Rohit04121998/mAhTime/PCB_KiCAD/PDF/mAhTime-F.CrtYd.pdf

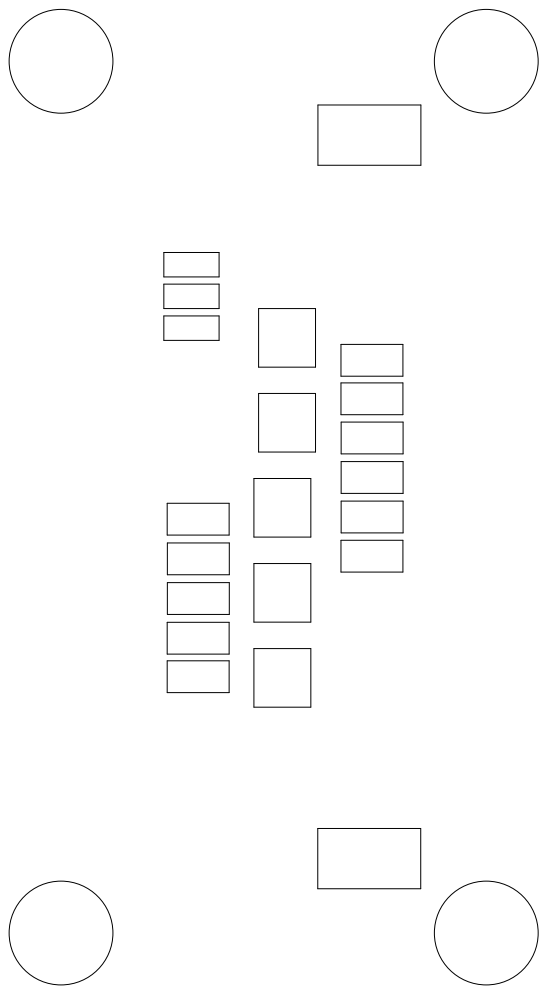
[picture p26: page 1]
