Rohit04121998/mAhTime/PCB_KiCAD/PDF/mAhTime-F.Cu.pdf

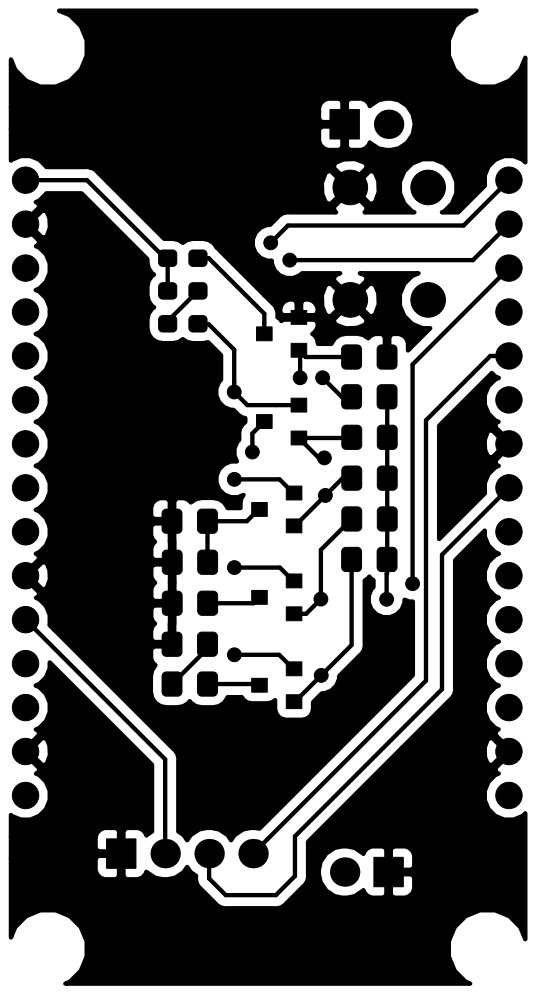
[picture p27: page 1]
