Rohit04121998/mAhTime/PCB_KiCAD/PDF/mAhTime-F.Fab.pdf

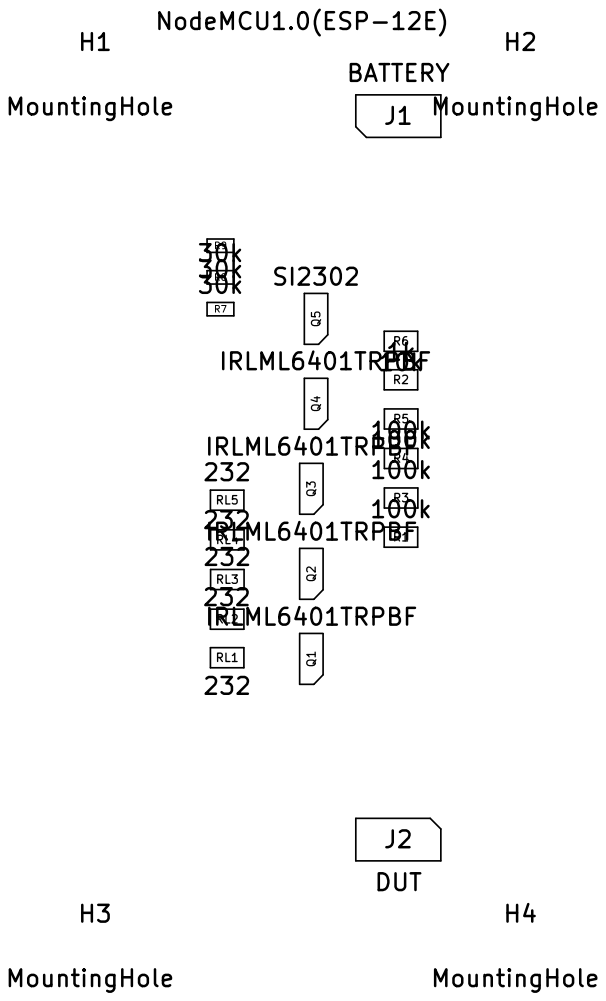
[picture p28: page 1]
