Rohit04121998/mAhTime/PCB_KiCAD/PDF/mAhTime-F.Mask.pdf

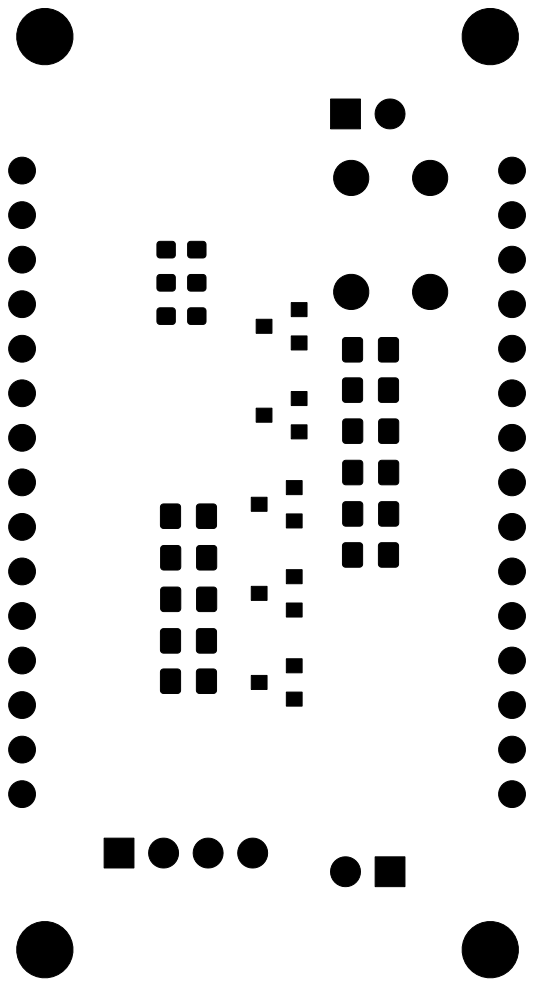
[picture p29: page 1]
