Rohit04121998/mAhTime/PCB_KiCAD/PDF/mAhTime-F.Paste.pdf

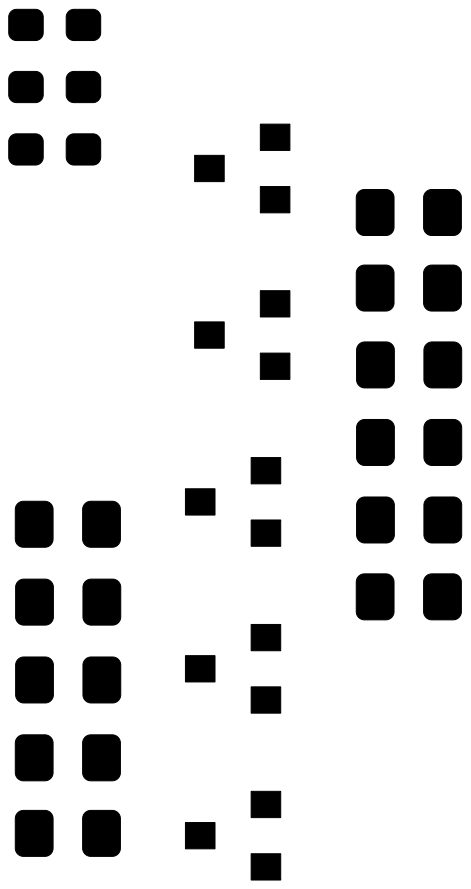
[picture p30: page 1]
