Rohit04121998/mAhTime/PCB_KiCAD/PDF/mAhTime-F.SilkS.pdf

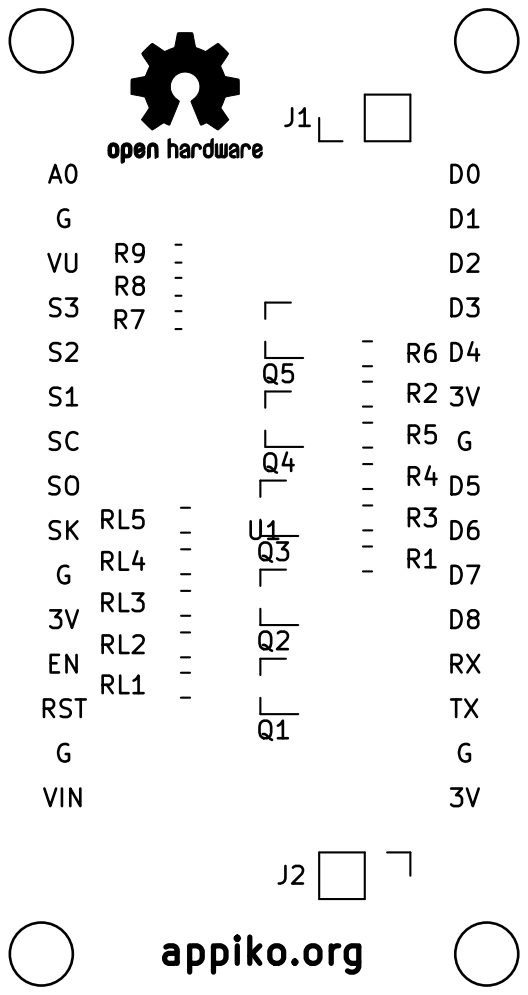
[picture p31: page 1]
