Rohit04121998/mAhTime/upload_voltage/displaySymbols.h

#define logo_width 128
#define logo_height 32
#define ohm_height 12
#define ohm_width 16
#define wifi_height 9
#define wifi_width 16

static const unsigned char PROGMEM logo[]= {      //logo shown during power up
0x00, 0x00, 0x00, 0x03, 0xE0, 0x00, 0x00, 0x00, 0x00, 0x00, 0x00, 0x00, 0x00, 0x00, 0x00, 0x00,
0x00, 0x00, 0x00, 0x1F, 0xF8, 0x00, 0x00, 0x00, 0x00, 0x00, 0x00, 0x00, 0x00, 0x00, 0x00, 0x00,
0x00, 0x00, 0x00, 0x7F, 0xFE, 0x00, 0x00, 0x00, 0x00, 0x00, 0x00, 0x00, 0x00, 0x00, 0x00, 0x00,
0x00, 0x00, 0x01, 0xFF, 0xFF, 0x00, 0x00, 0x00, 0x00, 0x00, 0x00, 0x00, 0x00, 0x00, 0x00, 0x00,
0x00, 0x00, 0x07, 0xC0, 0xFF, 0x80, 0x00, 0x00, 0x00, 0x00, 0x00, 0x00, 0x00, 0x00, 0x00, 0x00,
0x00, 0x00, 0x06, 0x00, 0x3F, 0xC0, 0x00, 0x00, 0x00, 0x00, 0x00, 0x00, 0x00, 0x00, 0x00, 0x00,
0x00, 0x00, 0x0C, 0x00, 0x1F, 0xC0, 0x00, 0x00, 0x00, 0x00, 0x04, 0x30, 0x00, 0x00, 0x00, 0x00,
0x00, 0x00, 0x0F, 0xF8, 0x19, 0xE0, 0x00, 0x00, 0x00, 0x00, 0x0E, 0x30, 0x00, 0x00, 0x00, 0x00,
0x00, 0x00, 0x10, 0x06, 0x19, 0xE0, 0x00, 0x00, 0x00, 0x00, 0x0E, 0x30, 0x00, 0x00, 0x00, 0x00,
0x00, 0x00, 0x00, 0x01, 0x3F, 0xE0, 0x00, 0x00, 0x00, 0x00, 0x00, 0x30, 0x00, 0x00, 0x00, 0x00,
0x00, 0x00, 0x00, 0x00, 0xFF, 0xE0, 0x00, 0x00, 0x00, 0x00, 0x00, 0x30, 0x00, 0x00, 0x00, 0x00,
0x00, 0x00, 0x00, 0x00, 0xFF, 0xE0, 0x0F, 0xC6, 0x78, 0xCF, 0x0E, 0x37, 0x83, 0xE0, 0x00, 0x00,
0x00, 0x00, 0x00, 0x00, 0xFF, 0xE0, 0x1F, 0xE6, 0xFC, 0xDF, 0x8E, 0x3F, 0xC7, 0xF0, 0x00, 0x00,
0x00, 0x00, 0x00, 0x01, 0xFF, 0xE0, 0x38, 0x67, 0x8C, 0xF9, 0x8E, 0x38, 0xCE, 0x38, 0x00, 0x00,
0x00, 0x00, 0x00, 0x01, 0xFF, 0xC0, 0x30, 0x67, 0x0E, 0xE1, 0xCE, 0x31, 0x8C, 0x18, 0x00, 0x00,
0x00, 0x00, 0x00, 0x01, 0xFF, 0xC0, 0x70, 0xC6, 0x06, 0xC0, 0xCE, 0x3F, 0x0C, 0x18, 0x00, 0x00,
0x00, 0x00, 0x00, 0x01, 0xFF, 0xE0, 0x71, 0xC6, 0x0C, 0xC1, 0x8E, 0x33, 0x8C, 0x18, 0x00, 0x00,
0x00, 0x00, 0x00, 0x00, 0xFF, 0xF0, 0x73, 0xC6, 0x1C, 0xC3, 0x8E, 0x31, 0xCE, 0x38, 0x00, 0x00,
0x00, 0x00, 0x00, 0x00, 0xFF, 0x00, 0x3E, 0xE7, 0xF0, 0xFE, 0x07, 0x30, 0xC7, 0xF0, 0x00, 0x00,
0x00, 0x00, 0x00, 0x00, 0xFC, 0x04, 0x0C, 0x47, 0xC0, 0xF8, 0x02, 0x30, 0xC3, 0xE0, 0x00, 0x00,
0x00, 0x00, 0x00, 0x00, 0x78, 0x04, 0x00, 0x03, 0x00, 0x60, 0x00, 0x00, 0x00, 0x00, 0x00, 0x00,
0x00, 0x00, 0x00, 0x00, 0x30, 0x06, 0x00, 0x03, 0x00, 0x60, 0x00, 0x00, 0x00, 0x00, 0x00, 0x00,
0x00, 0x00, 0x00, 0x00, 0x20, 0x0E, 0x00, 0x03, 0x00, 0x60, 0x00, 0x00, 0x00, 0x00, 0x00, 0x00,
0x00, 0x00, 0x00, 0x00, 0x40, 0x1E, 0x00, 0x03, 0x00, 0x60, 0x00, 0x00, 0x00, 0x00, 0x00, 0x00,
0x00, 0x00, 0x00, 0x00, 0x80, 0x3E, 0x00, 0x03, 0x00, 0x60, 0x00, 0x00, 0x00, 0x00, 0x00, 0x00,
0x00, 0x00, 0x00, 0x01, 0x00, 0x7F, 0x00, 0x00, 0x00, 0x00, 0x00, 0x00, 0x00, 0x00, 0x00, 0x00,
0x00, 0x00, 0x00, 0x00, 0xC1, 0xFF, 0x00, 0x00, 0x00, 0x00, 0x00, 0x00, 0x00, 0x00, 0x00, 0x00,
0x00, 0x00, 0x00, 0x00, 0x3F, 0xFF, 0x00, 0x00, 0x00, 0x00, 0x00, 0x00, 0x00, 0x00, 0x00, 0x00,
0x00, 0x00, 0x00, 0x00, 0x01, 0xFF, 0x00, 0x00, 0x00, 0x00, 0x00, 0x00, 0x00, 0x00, 0x00, 0x00,
0x00, 0x00, 0x00, 0x00, 0x00, 0x3F, 0x00, 0x00, 0x00, 0x00, 0x00, 0x00, 0x00, 0x00, 0x00, 0x00,
0x00, 0x00, 0x00, 0x00, 0x00, 0x13, 0x00, 0x00, 0x00, 0x00, 0x00, 0x00, 0x00, 0x00, 0x00, 0x00,
0x00, 0x00, 0x00, 0x00, 0x00, 0x13, 0x00, 0x00, 0x00, 0x00, 0x00, 0x00, 0x00, 0x00, 0x00, 0x00
};

static const unsigned char PROGMEM ohm [] = {     //symbol for ohm
  B00000111, B11100000,
  B00011111, B11111000,
  B00111100, B00111100,
  B01111000, B00011110,
  B01110000, B00001110,
  B01110000, B00001110,
  B00111000, B00011100,
  B00011100, B00111000,
  B00001100, B00110000,
  B10000110, B01100001,
  B11000110, B01100011,
  B11111100, B00111111,
};

static const unsigned char PROGMEM wifi [] = {
  B00000111, B11100000,
  B00001000, B00010000,
  B00010011, B11001000,
  B00000100, B00100000,
  B00000001, B10000000,
  B00000010, B01000000,
  B00000000, B00000000,
  B00000001, B10000000,
  B00000001, B10000000,
};
