Rohit04121998/mAhTime/upload_voltage/DateTime.h

#include <NTPClient.h>
#include <ESP8266WiFi.h>
#include <WiFiUdp.h>

// Define NTP Client to get time
WiFiUDP ntpUDP;
NTPClient timeClient(ntpUDP);

// Variables to save date and time
String formattedDate;
String dayStamp;
String timeStamp;
String datetime = "";

String dateTime() {  
  // Initialize a NTPClient to get time
  timeClient.begin();
  // Set offset time in seconds to adjust for your timezone, for example:
  // GMT +1 = 3600
  // GMT +8 = 28800
  // GMT -1 = -3600
  // GMT 0 = 0
  timeClient.setTimeOffset(19800);

  while(!timeClient.update()) {
    timeClient.forceUpdate();
  }
  // The formattedDate comes with the following format:
  // 2018-05-28T16:00:13Z
  // We need to extract date and time
  formattedDate = timeClient.getFormattedDate();

  // Extract date
  int splitT = formattedDate.indexOf("T");
  dayStamp = formattedDate.substring(0, splitT);
  // Extract time
  timeStamp = formattedDate.substring(splitT+1, formattedDate.length()-1);
  delay(1000);
  datetime = datetime + dayStamp + "_" + timeStamp;
  return datetime;
}
